freeDSP/FreeDSP-G/kiCAD/FreeDSP-G_MAIN/Rendering/FreeDSP-G_FlipView.jpg

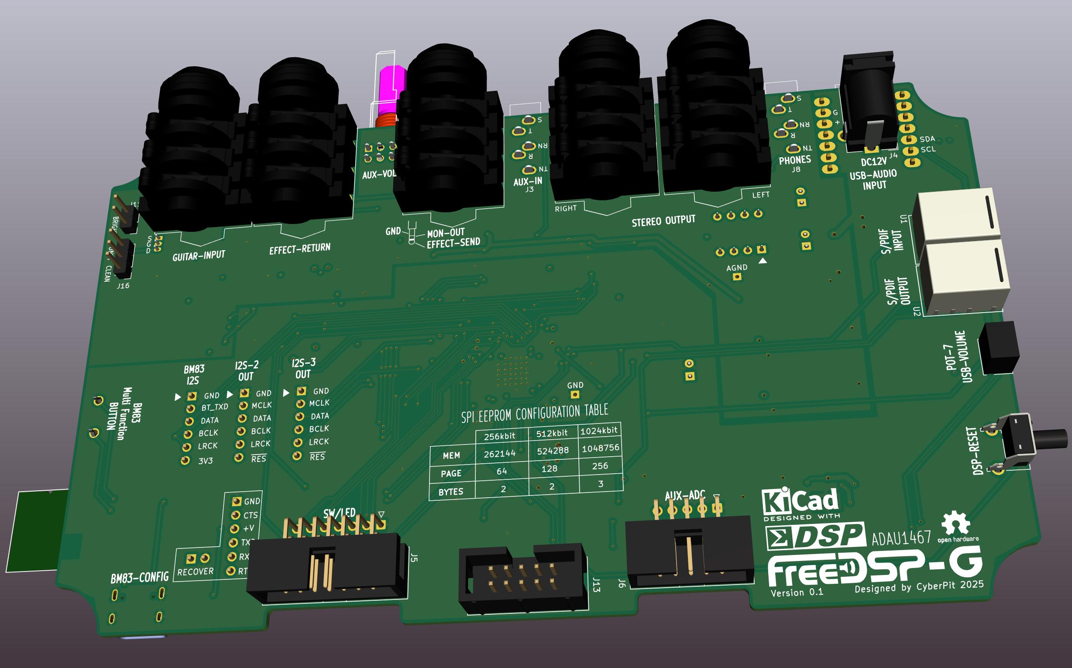
kiCAD/FreeDSP-G_MAIN/Rendering/FreeDSP-G_FlipView.jpg
