freeDSP/FreeDSP-G/kiCAD/FreeDSP-G_MAIN/Rendering/FreeDSP-G_ImageView2.jpg

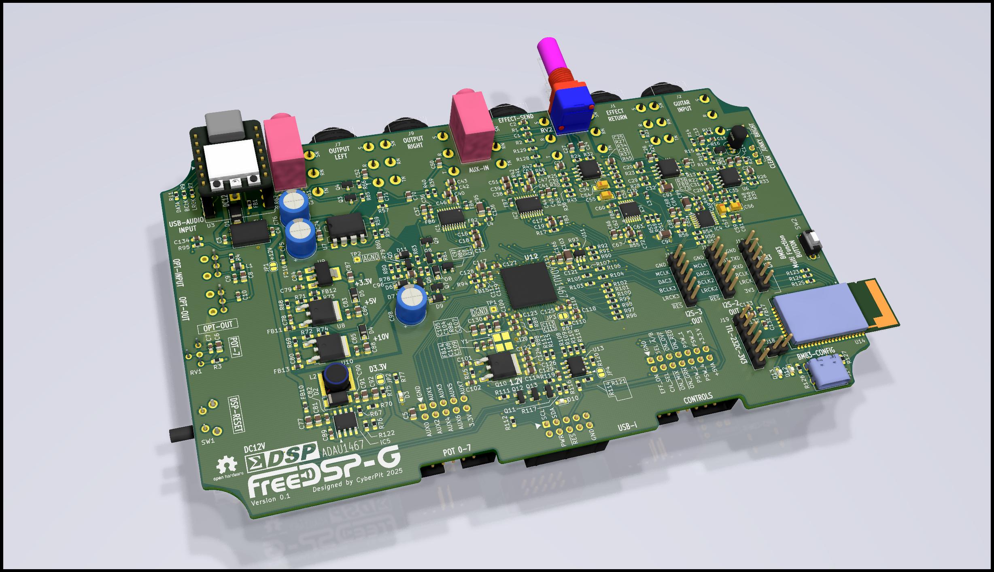
kiCAD/FreeDSP-G_MAIN/Rendering/FreeDSP-G_ImageView2.jpg
