freeDSP/FreeDSP-G/kiCAD/FreeDSP-G_MAIN/Rendering/FreeDSP-G_ImageView.jpg

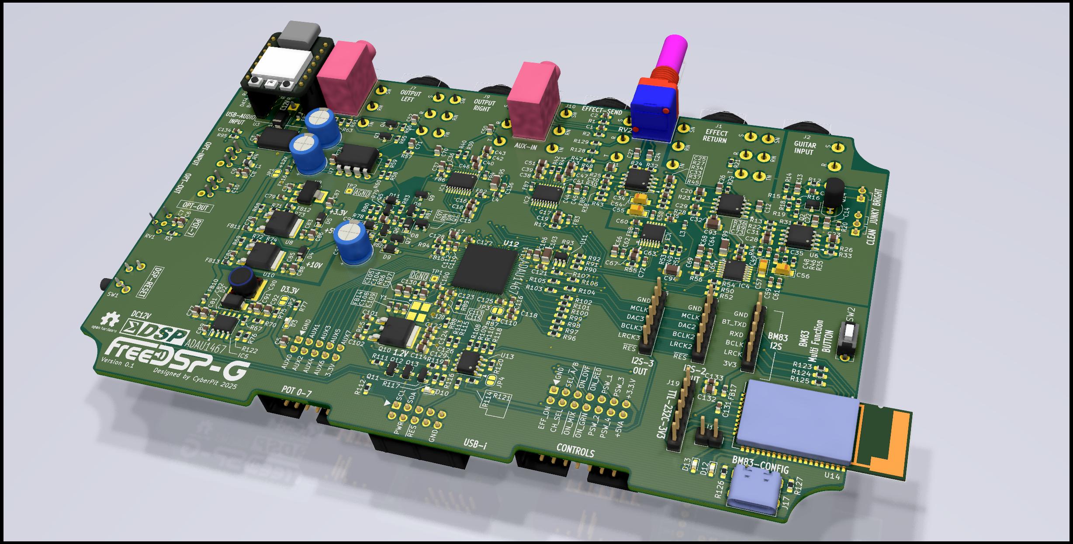
kiCAD/FreeDSP-G_MAIN/Rendering/FreeDSP-G_ImageView.jpg
