freeDSP/FreeDSP-G/kiCAD/FreeDSP-G_MAIN/Rendering/FreeDSP-G_RearView.jpg

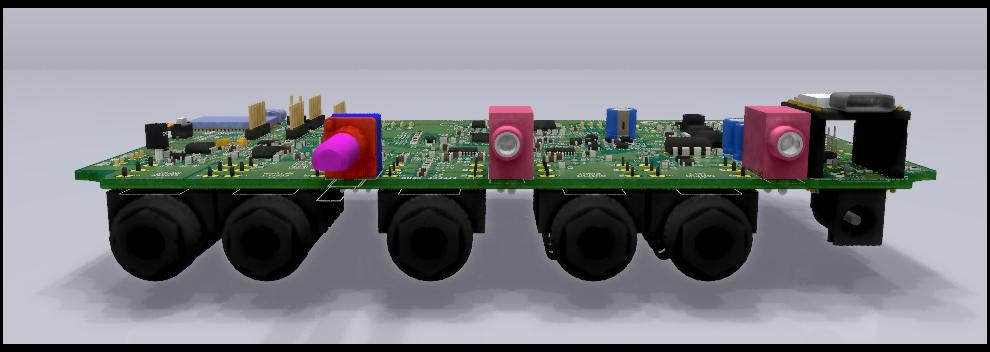
kiCAD/FreeDSP-G_MAIN/Rendering/FreeDSP-G_RearView.jpg
