freeDSP/FreeDSP-G/kiCAD/FreeDSP-G_MAIN/Rendering/FreeDSP-G_RightFrontView.jpg

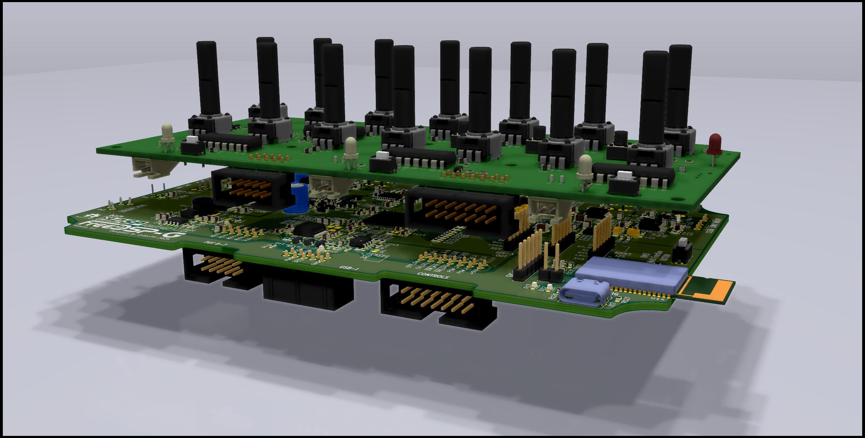
kiCAD/FreeDSP-G_MAIN/Rendering/FreeDSP-G_RightFrontView.jpg
