freeDSP/FreeDSP-G/kiCAD/FreeDSP-G_MAIN/Rendering/FreeDSP-G_Stacked_Rear.jpg

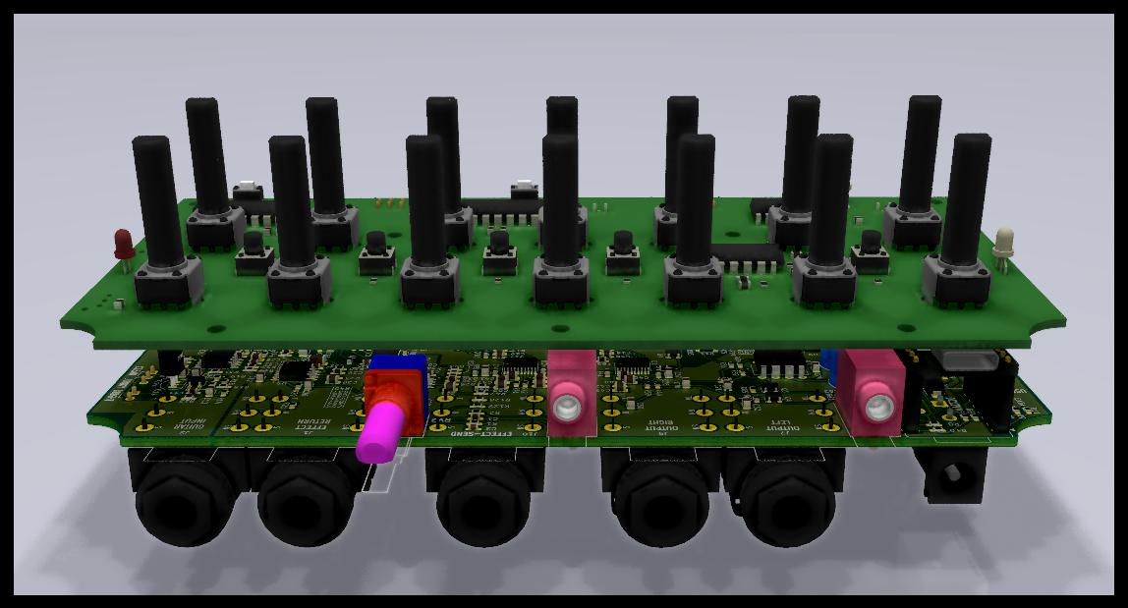
kiCAD/FreeDSP-G_MAIN/Rendering/FreeDSP-G_Stacked_Rear.jpg
