freeDSP/FreeDSP-G/kiCAD/FreeDSP-G_MAIN/Rendering/FreeDSP-G_Stacked_TopView.jpg

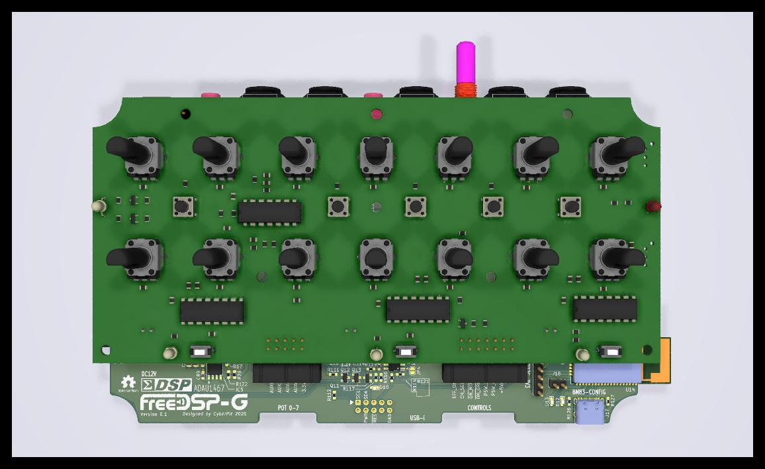
kiCAD/FreeDSP-G_MAIN/Rendering/FreeDSP-G_Stacked_TopView.jpg
