freeDSP/FreeDSP-G/kiCAD/FreeDSP-G_POT-SWITCH/3D-Rendering/POT_SWITCH_TopView.jpg

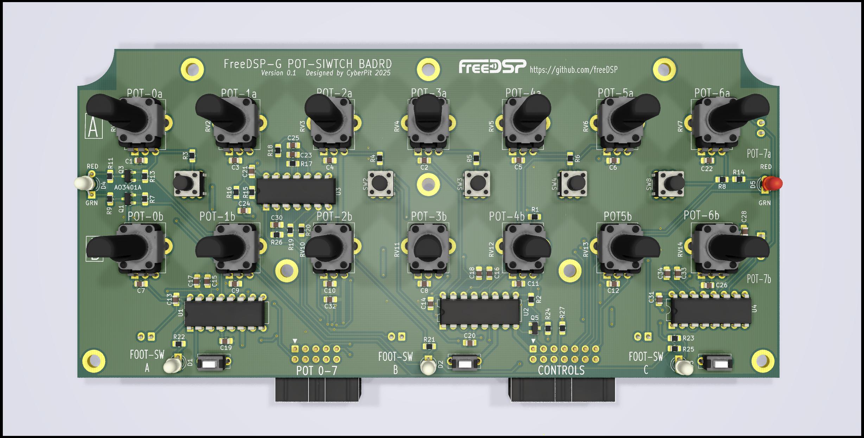
kiCAD/FreeDSP-G_POT-SWITCH/3D-Rendering/POT_SWITCH_TopView.jpg
