freeDSP/FreeDSP-G/SigmaStudio/IR-Files/IR-Waves.png

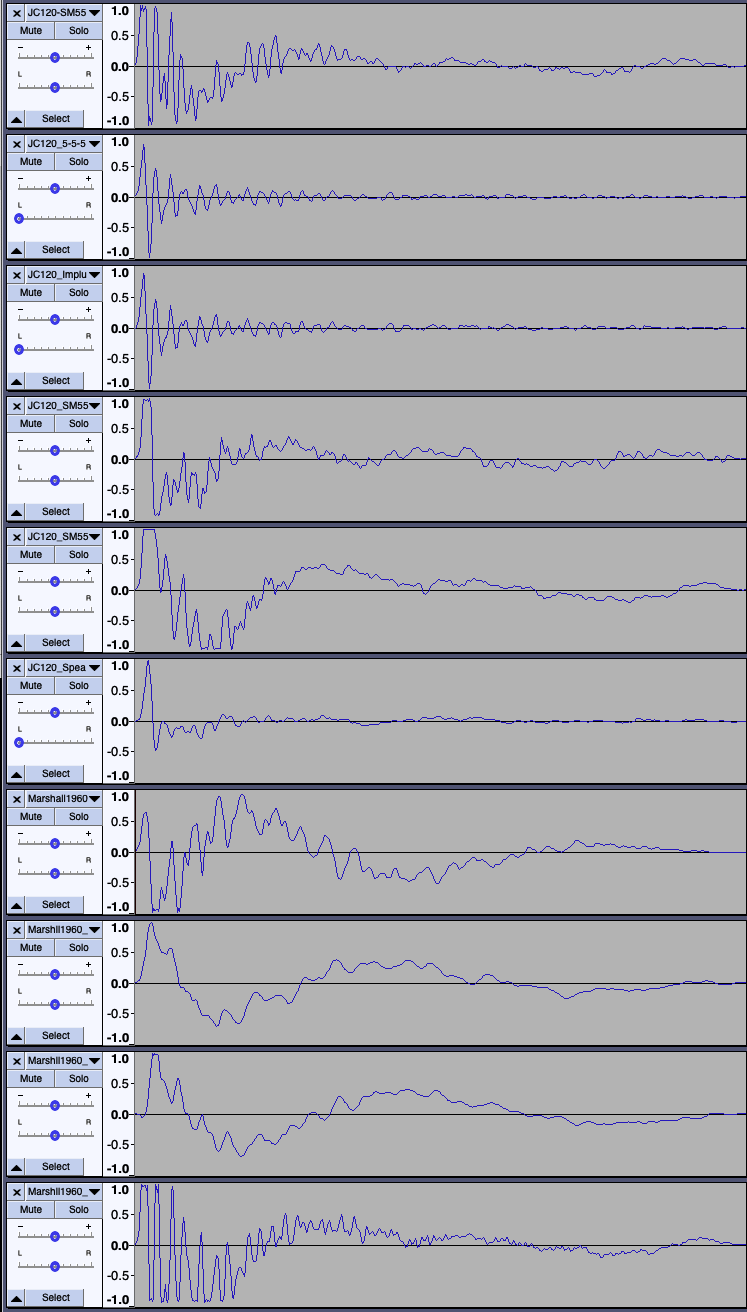
SigmaStudio/IR-Files/IR-Waves.png
