freeDSP/FreeDSP-G/kiCAD/FreeDSP-G_POT-SWITCH/POT_SWITCH_0v1_BOM-ALL.xlsx

Sheet: PCBA
Designator | Quantity | Package | Designation | JLCPCB#
C32 | 1 | C_0805_2012Metric_Pad1.18x1.45mm_HandSolder | 10uF | C15850
C34,C33,C20,C19,C18,C17,C16,C15 | 8 | C_0805_2012Metric_Pad1.18x1.45mm_HandSolder | 0.01uF | C1710
C6,C31,C30,C28,C27,C26,C25,C24,C23,C22,C21,C14,C13,C12,C11,C10,C9,C8,C7,C5,C4,C3,C2,C1 | 24 | C_0805_2012Metric_Pad1.18x1.45mm_HandSolder | 0.1uF | C49678
Q3,Q1 | 2 | SOT-23-3 | AO3401A | C15127
Q5 | 1 | SOT-23 | AO3400A | C20917
R1 | 1 | R_0805_2012Metric_Pad1.20x1.40mm_HandSolder | 0R | C17477
R18,R17 | 2 | R_0805_2012Metric_Pad1.20x1.40mm_HandSolder | 1MEG | C17514
R20 | 1 | R_0805_2012Metric_Pad1.20x1.40mm_HandSolder | 1k | C17513
R23,R22,R21,R14,R11,R9 | 6 | R_0805_2012Metric_Pad1.20x1.40mm_HandSolder | 330R | C17630
R25,R19 | 2 | R_0805_2012Metric_Pad1.20x1.40mm_HandSolder | 2.2k | C17520
R27,R26 | 2 | R_0805_2012Metric_Pad1.20x1.40mm_HandSolder | 3.3k | C26010
R8,R24,R16,R15,R13,R7,R6,R5,R4,R3 | 10 | R_0805_2012Metric_Pad1.20x1.40mm_HandSolder | 10k | C17414

Sheet: HAND
Designator | Quantity | Package | Designation | JLCPCB#
D3,D2,D1 | 3 | LED_D3.0mm_Clear | LED | HAND
D4 | 1 | Dual Color LED_D3.0mm-3 | LED_RED-GRN | HAND
D5 | 1 | LED_D3.0mm | LED_RED | HAND
J3,J2,J1 | 3 | JST_XH_S2B-XH-A_1x02_P2.50mm_Horizontal | JST_S2B-XH | HAND
J4 | 1 | IDC-Header_2x07_P2.54mm_Horizontal | Conn_02x07_Odd_Even | HAND
J7 | 1 | IDC-Header_2x05_P2.54mm_Horizontal | Conn_02x05_Odd_Even | HAND
RV14,RV13,RV12,RV11,RV10,RV9,RV8,RV7,RV6,RV5,RV4,RV3,RV2,RV1 | 14 | Alps_RK09K113 | B10K | HAND
U3 | 1 | DIP-14_W7.62mm | 74HC74 | HAND
U4,U2,U1 | 3 | DIP-16_W7.62mm | 74HC4053D | HAND
SW8,SW4,SW3,SW2,SW1 | 5 | PUSHSW_DPDT_6-7mm | PB-22E60L 2mm-DPDT | HAND
J6,J5 | 2 | JST_XH_B3B-XH-A_1x03_P2.50mm_Vertical | NOP | NOP
R2 | 1 | R_0805_2012Metric_Pad1.20x1.40mm_HandSolder | NOP | NOP
SW7,SW6,SW5 | 3 | MJTP1250 (for Debug Only) | NOP | NOP
