freeDSP/FreeDSP-G/kiCAD/FreeDSP-G_MAIN/JLCPCB_OrderFIles/277622863282176-Produce_DanZh2i.SMT_Snapshot.Top.3093181A_Y52.SMT025020160721.png

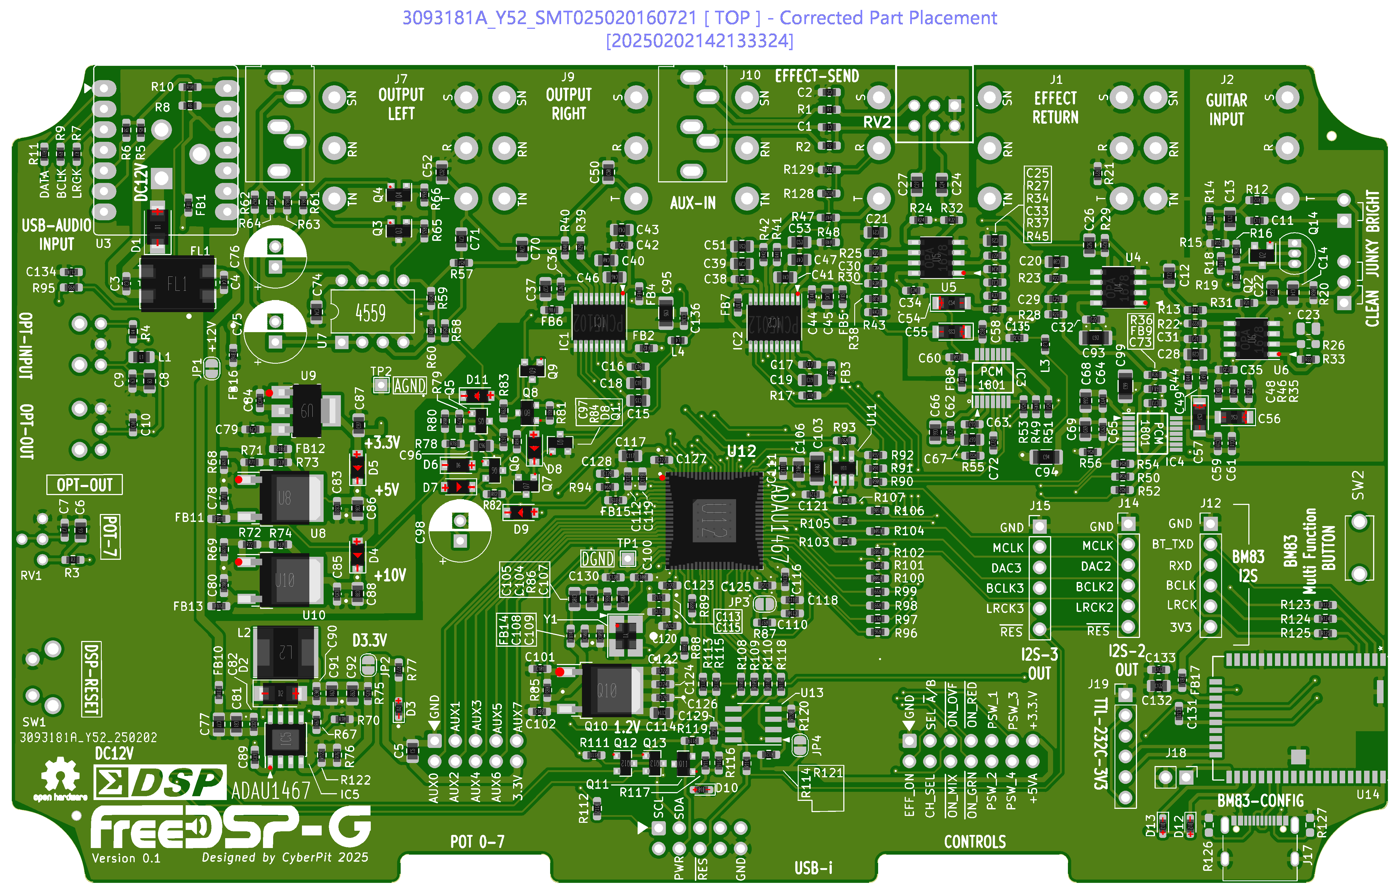
kiCAD/FreeDSP-G_MAIN/JLCPCB_OrderFIles/277622863282176-Produce_DanZh2i.SMT_Snapshot.Top.3093181A_Y52.SMT025020160721.png
